TallerDeProyecto1/rescatar/Software/inc/Main.h

/* Copyright 2014, Mariano Cerdeiro
 * Copyright 2014, Pablo Ridolfi
 * Copyright 2014, Juan Cecconi
 * Copyright 2014, Gustavo Muro
 *
 * This file is part of CIAA Firmware.
 *
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
 * 3. Neither the name of the copyright holder nor the names of its
 *    contributors may be used to endorse or promote products derived from this
 *    software without specific prior written permission.
 *
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
 */

#ifndef _ciaa_i2c_master_H_
#define _ciaa_i2c_master_H_
/** \brief Blinking example header file
 **
 ** This is a mini example of the CIAA Firmware
 **
 **/

/** \addtogroup CIAA_Firmware CIAA Firmware
 ** @{ */
/** \addtogroup Examples CIAA Firmware Examples
 ** @{ */
/** \addtogroup Blinking Blinking example header file
 ** @{ */

/*
 * Initials     Name
 * ---------------------------
 *
 */

/*
 * modification history (new versions first)
 * -----------------------------------------------------------
 * yyyymmdd v0.0.1 initials initial version
 */

/*==================[inclusions]=============================================*/

/*==================[macros]=================================================*/

/*==================[typedef]================================================*/

/*==================[external data declaration]==============================*/

/*==================[external functions declaration]=========================*/

/** @} doxygen end group definition */
/** @} doxygen end group definition */
/** @} doxygen end group definition */
/*==================[end of file]============================================*/
#endif /* #ifndef _BLINKING_H_ */
